Scybin/scyboard/images/bottom_case.png

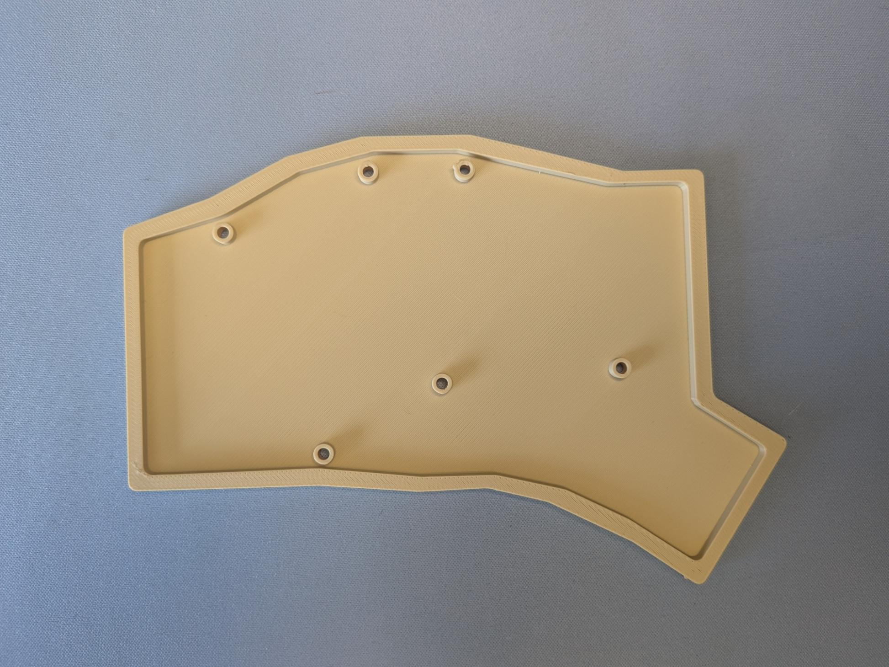
images/bottom_case.png
