Scybin/scyboard/images/matrix.png

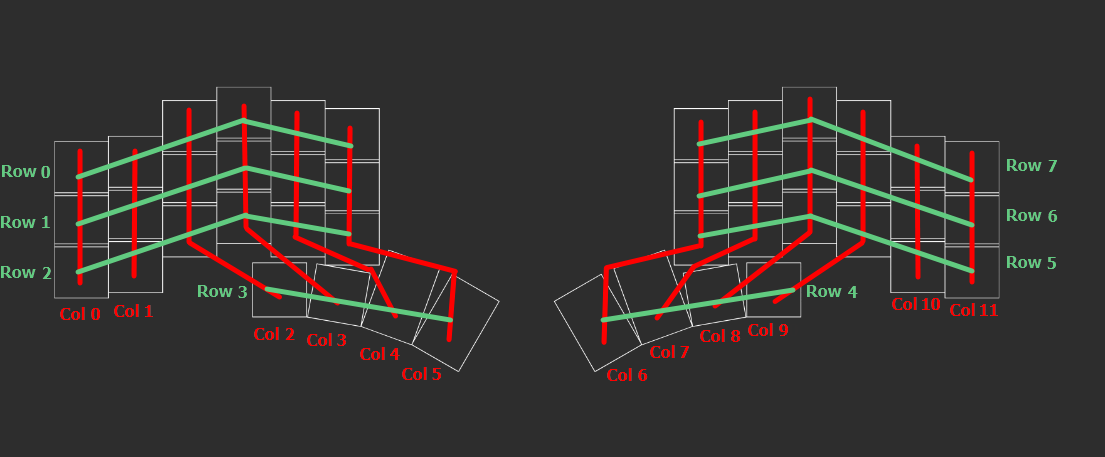
images/matrix.png
