Scybin/scyboard/images/pcb_top.png

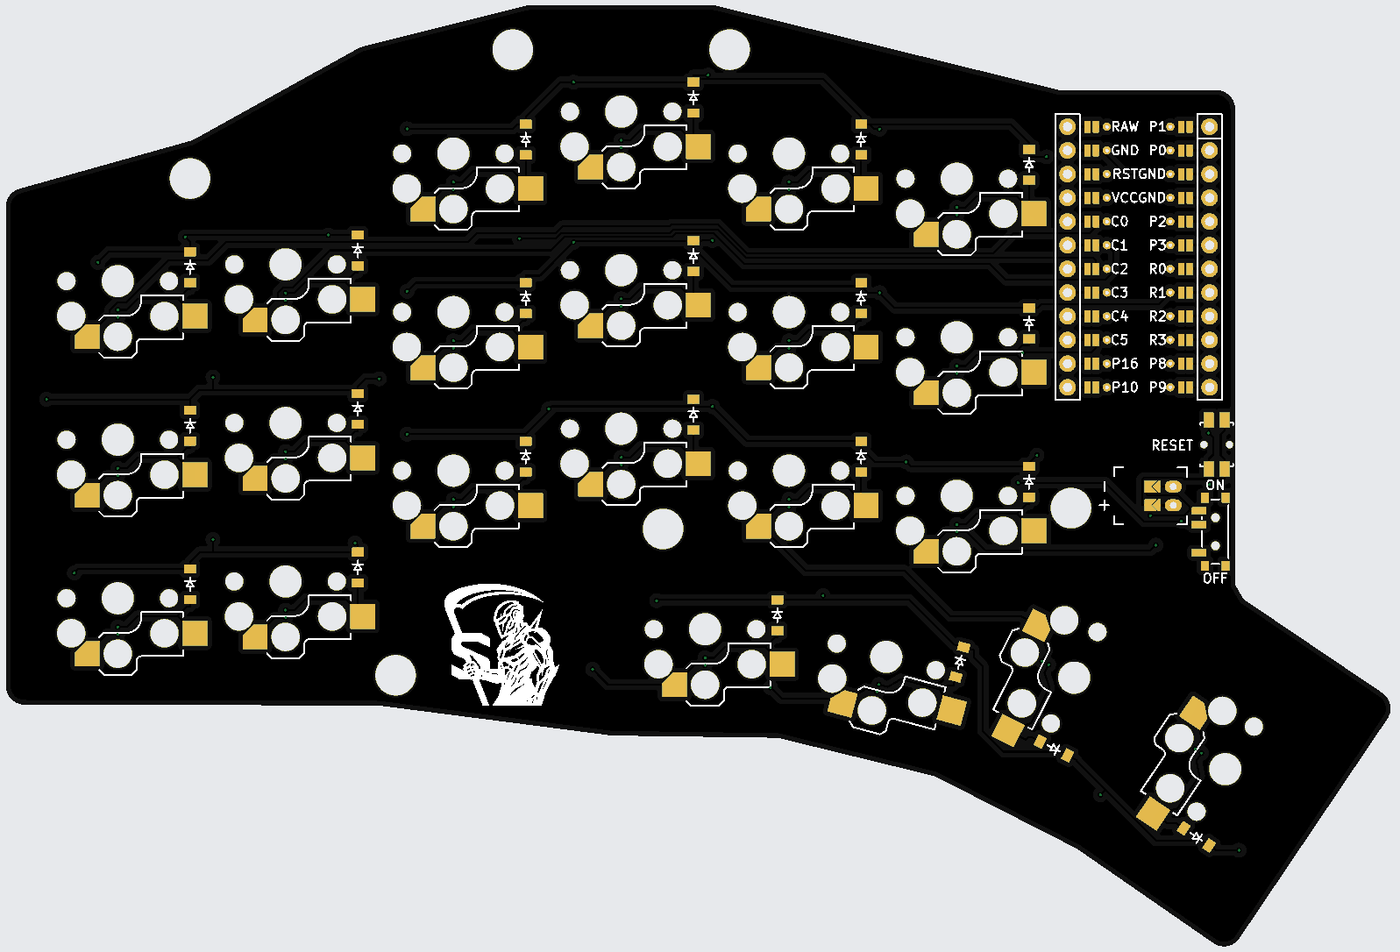
images/pcb_top.png
