Scybin/scyboard/images/scyboard.png

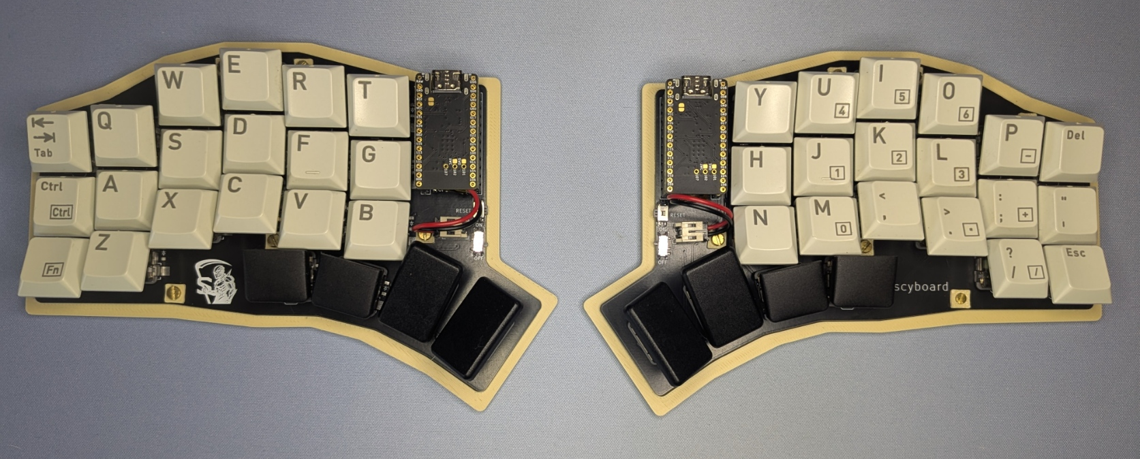
images/scyboard.png
