Scybin/scyboard/images/scyboard_plated.png

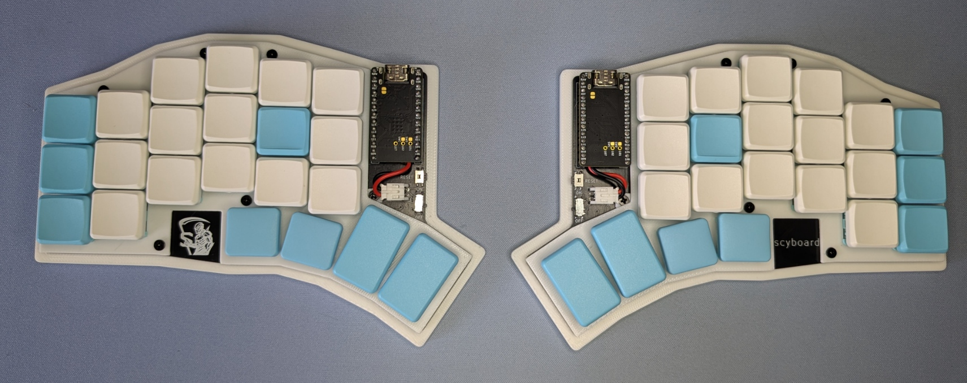
images/scyboard_plated.png
